IronReign/ffutse/images/FFUSE_Flat_Pattern_RC1.png

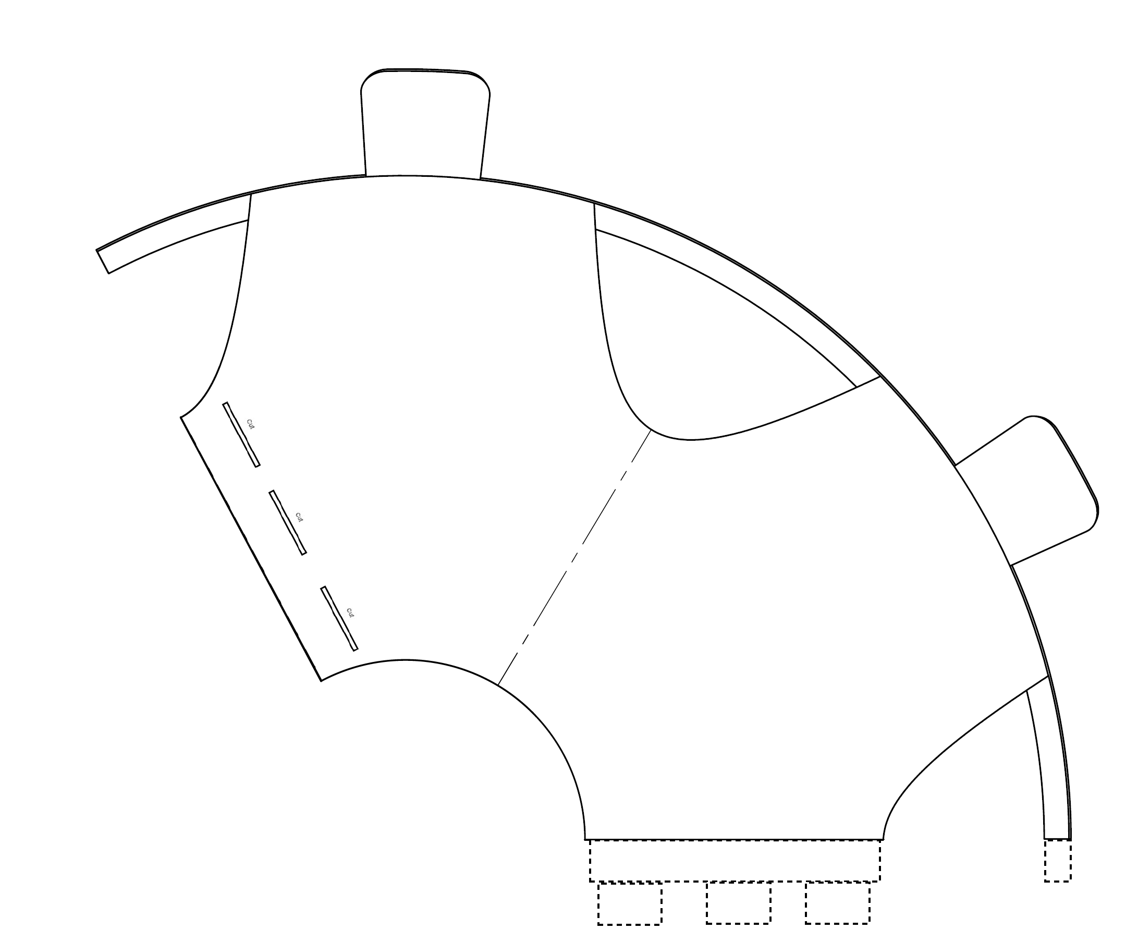
images/FFUSE_Flat_Pattern_RC1.png
