IronReign/ffutse/images/FFUTSE_Certified.png

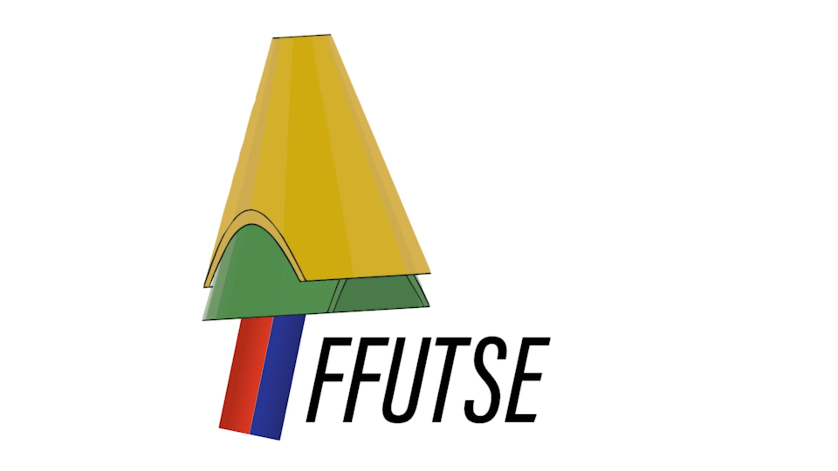
images/FFUTSE_Certified.png
