IronReign/ffutse/images/ffutse_reference_tabs.png

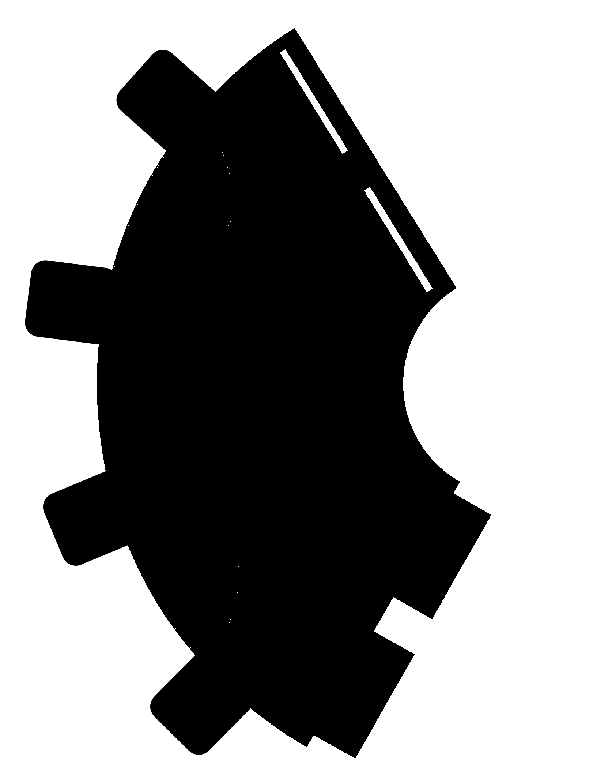
images/ffutse_reference_tabs.png
