IronReign/ffutse/images/freightfront.jpg

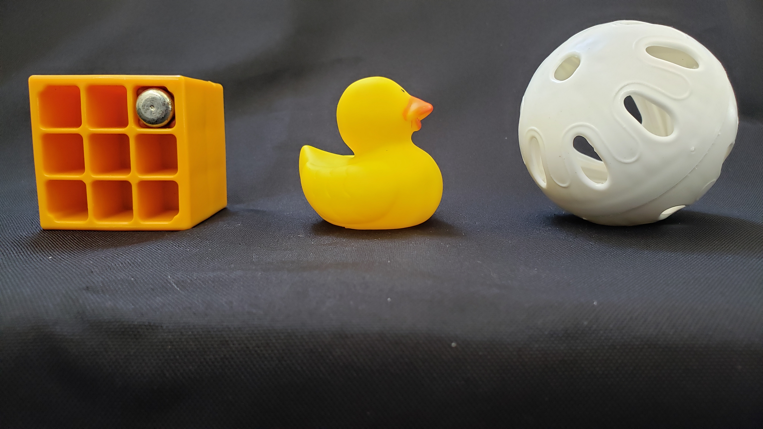
images/freightfront.jpg
