IronReign/ffutse/images/pattern3.jpg

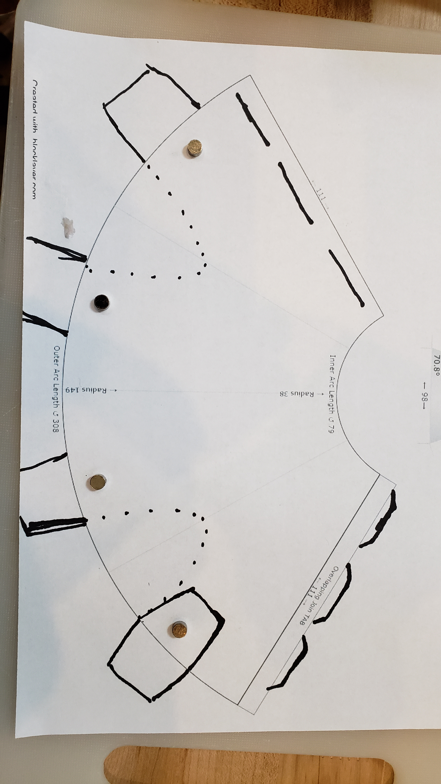
images/pattern3.jpg
